cypriani/keymini/cad/plate.2d.scad

use <lib.scad>;

plate();
